j3ster2019/HF-PA-v10/FuturePowerControl/Screenshot_2023-09-25_10-48-14.png

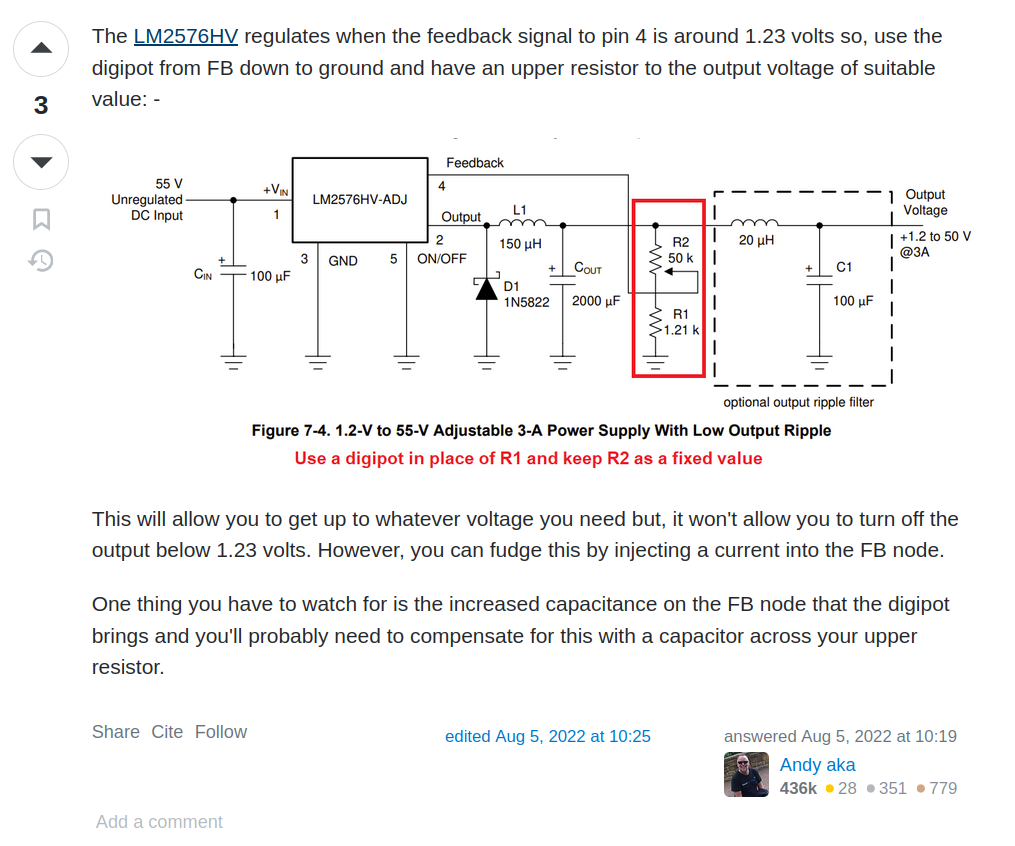
FuturePowerControl/Screenshot_2023-09-25_10-48-14.png
