j3ster2019/HF-PA-v10/Heat-Sinking/heatsinkmtg.gif

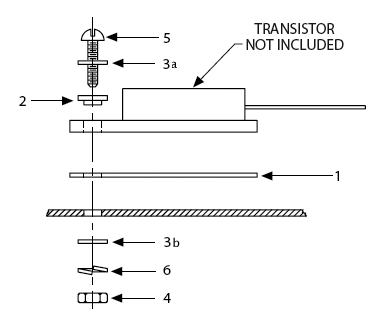
Heat-Sinking/heatsinkmtg.gif
