j3ster2019/HF-PA-v10/Heat-Sinking/heatsinkmtgparts.gif

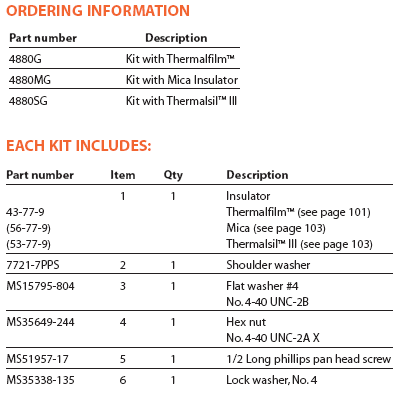
Heat-Sinking/heatsinkmtgparts.gif
