j3ster2019/HF-PA-v10/info/25wlinear-small.png

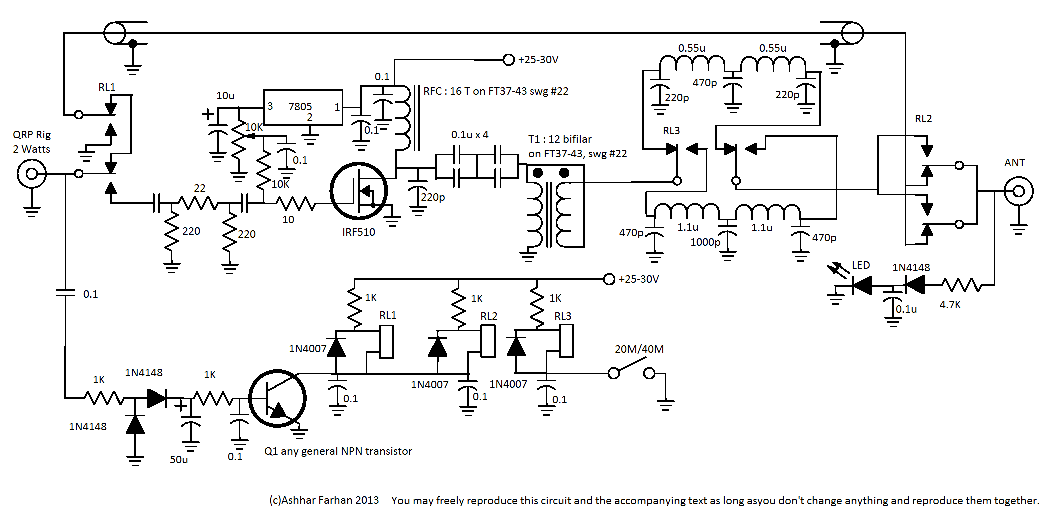
info/25wlinear-small.png
