j3ster2019/HF-PA-v10/info/Henning Paul's PA prototype.jpeg

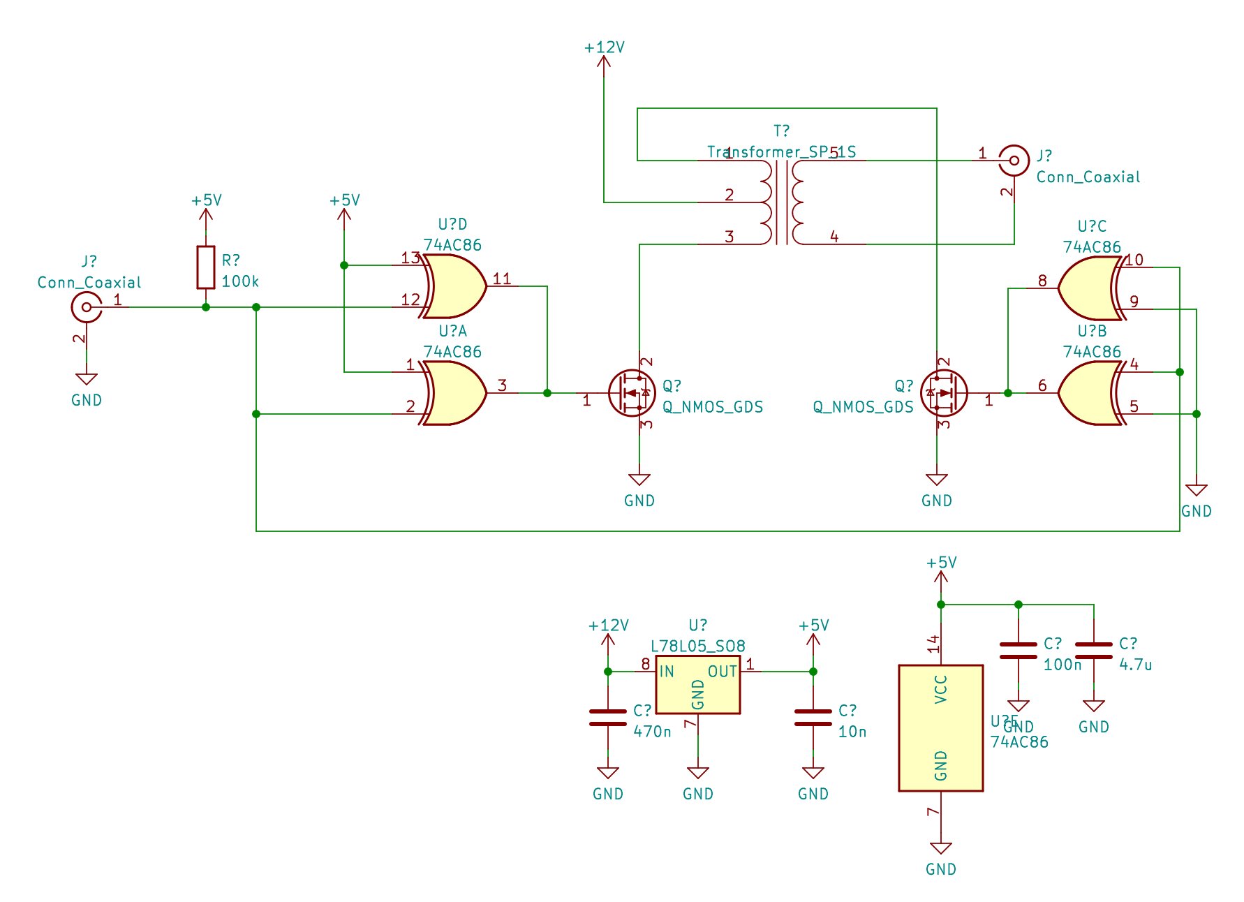
info/Henning Paul's PA prototype.jpeg
