j3ster2019/HF-PA-v10/info/Screenshot_2022-11-07_18-18-30.png

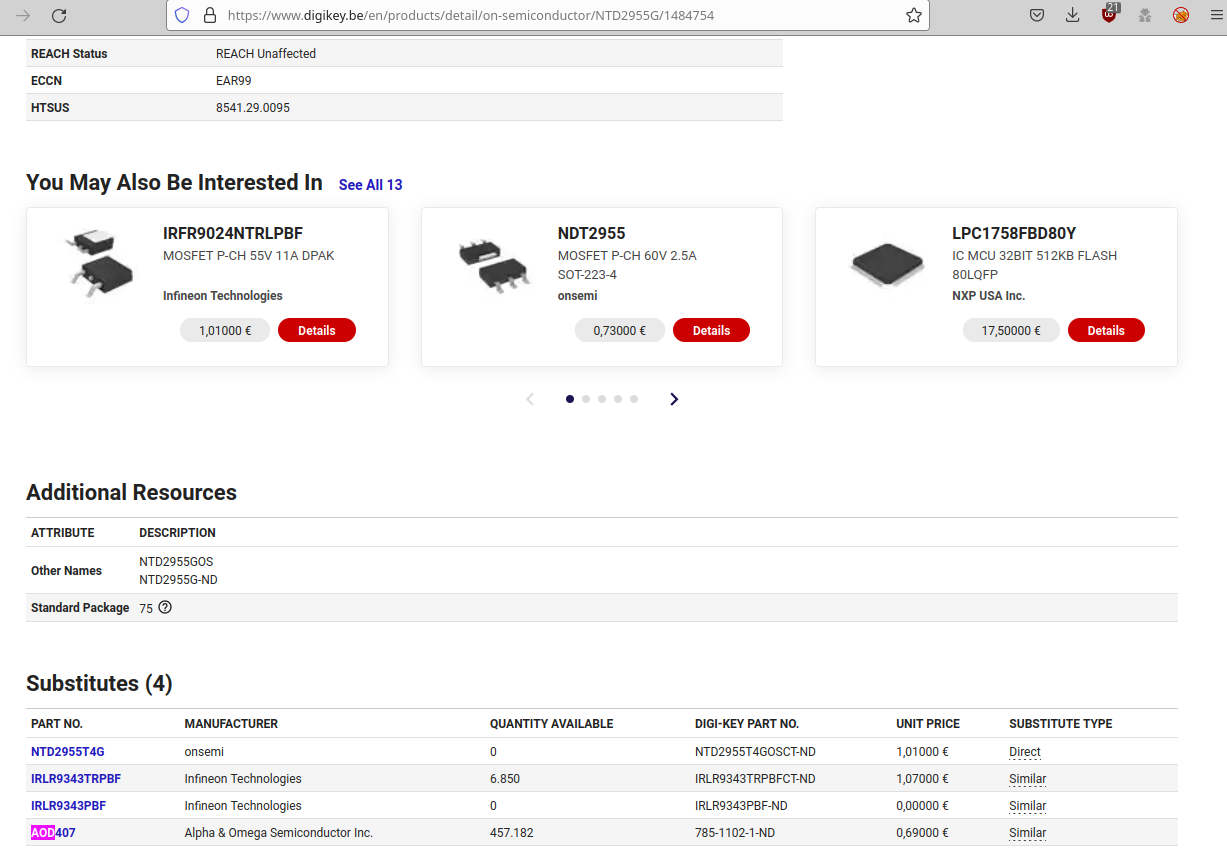
info/Screenshot_2022-11-07_18-18-30.png
