j3ster2019/HF-PA-v10/IRF530-Hack/Screenshot_2023-09-17_14-39-16.png

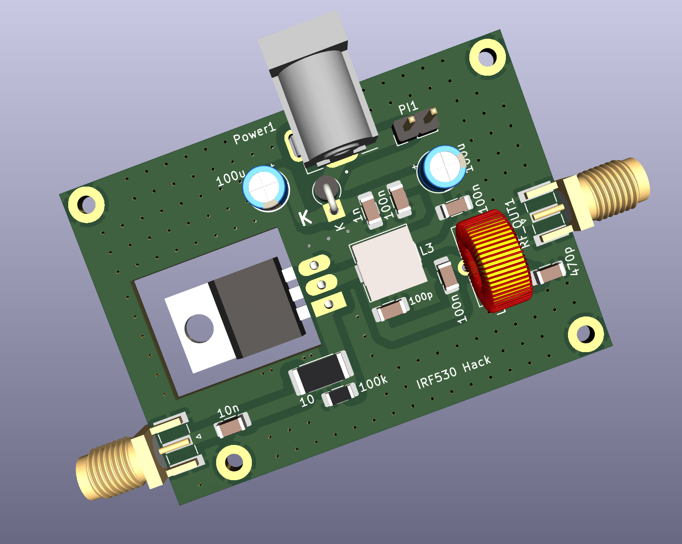
IRF530-Hack/Screenshot_2023-09-17_14-39-16.png
