j3ster2019/HF-PA-v10/IRFP-Hacks-v4/Screenshot_2024-04-25_09-21-08.png

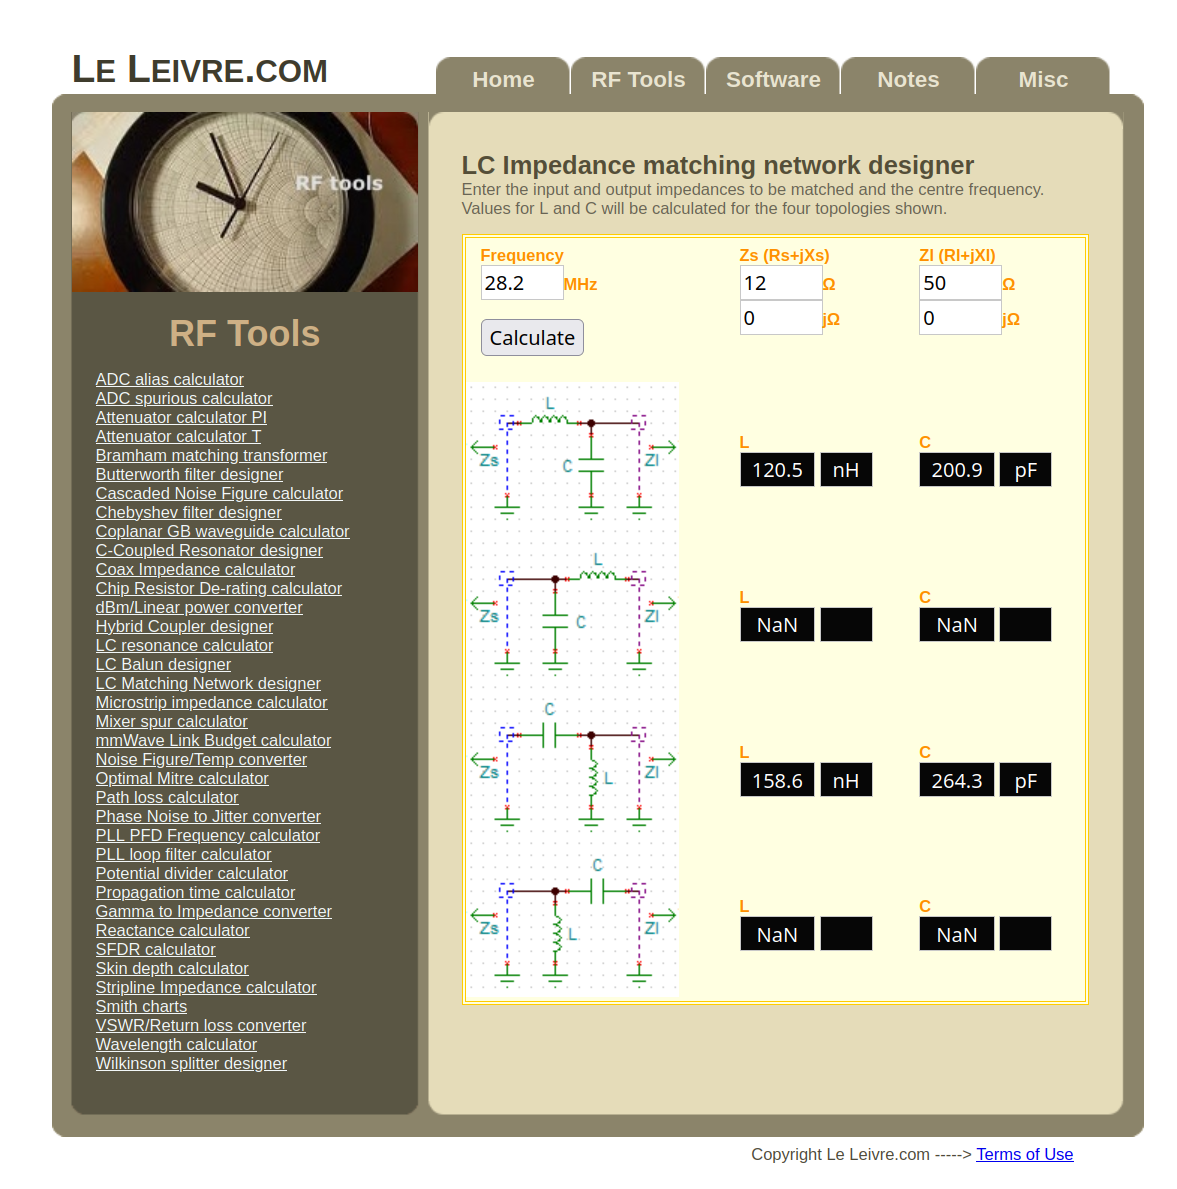
IRFP-Hacks-v4/Screenshot_2024-04-25_09-21-08.png
