j3ster2019/HF-PA-v10/IRFP-Hacks/Screenshot_2024-02-22_09-20-52.png

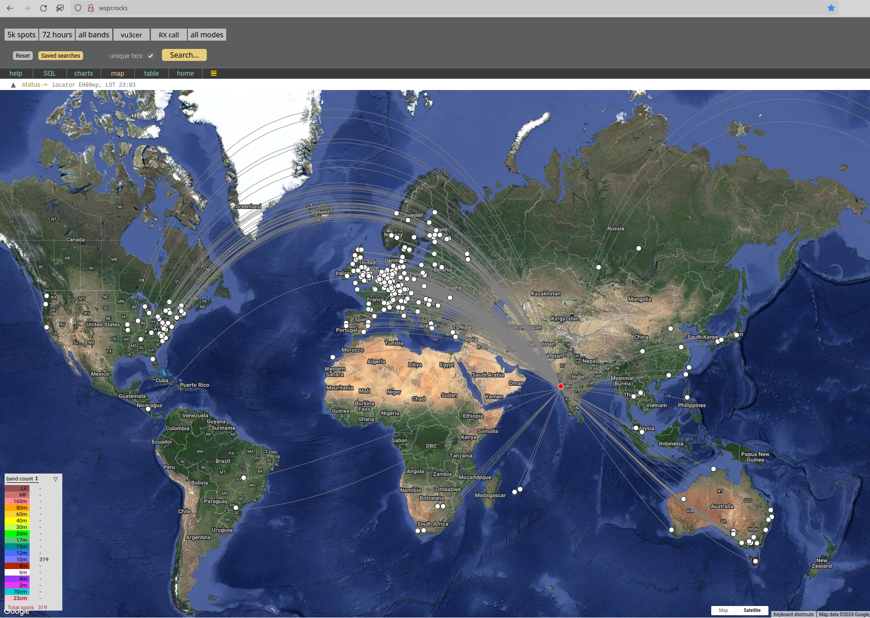
IRFP-Hacks/Screenshot_2024-02-22_09-20-52.png
