j3ster2019/HF-PA-v10/MRF101-Hack/7448510091.jpg

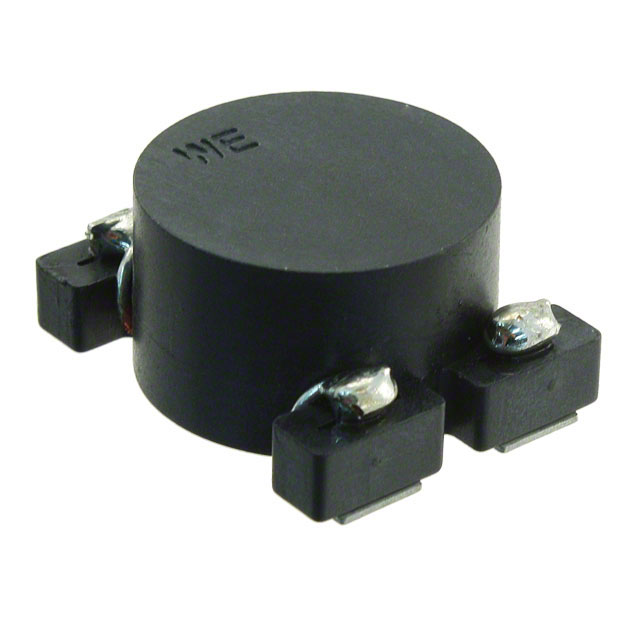
MRF101-Hack/7448510091.jpg
