j3ster2019/HF-PA-v10/R7/Screenshot_2023-10-06_10-12-58.png

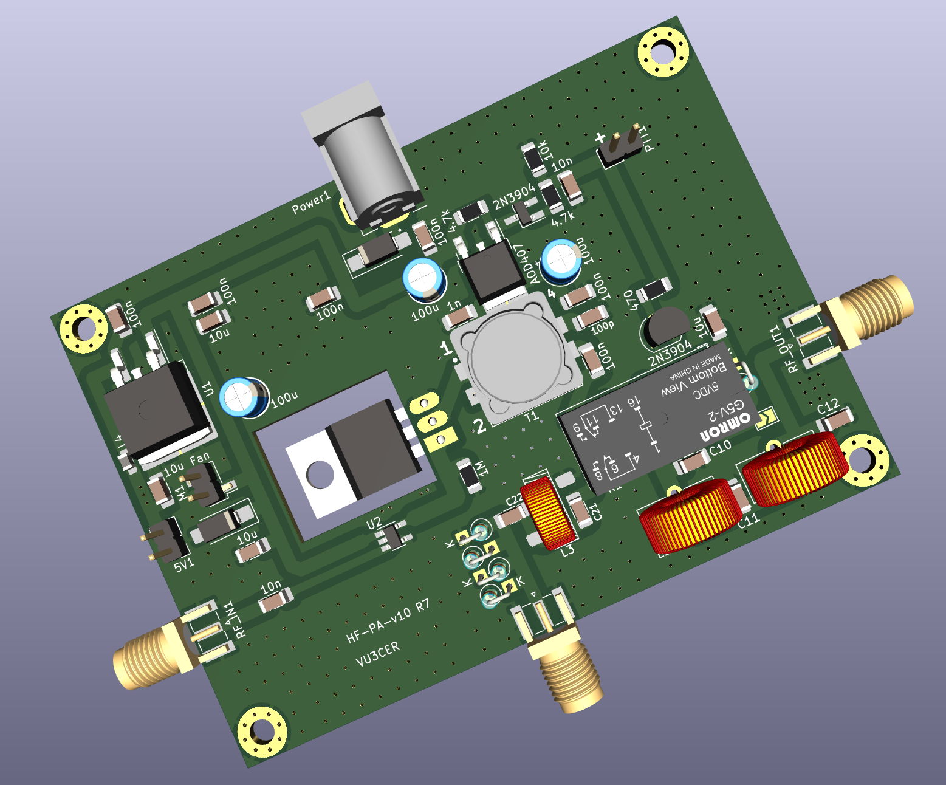
R7/Screenshot_2023-10-06_10-12-58.png
