j3ster2019/HF-PA-v10/v3-RD16HHF1/Screenshot_2023-09-16_10-33-11.png

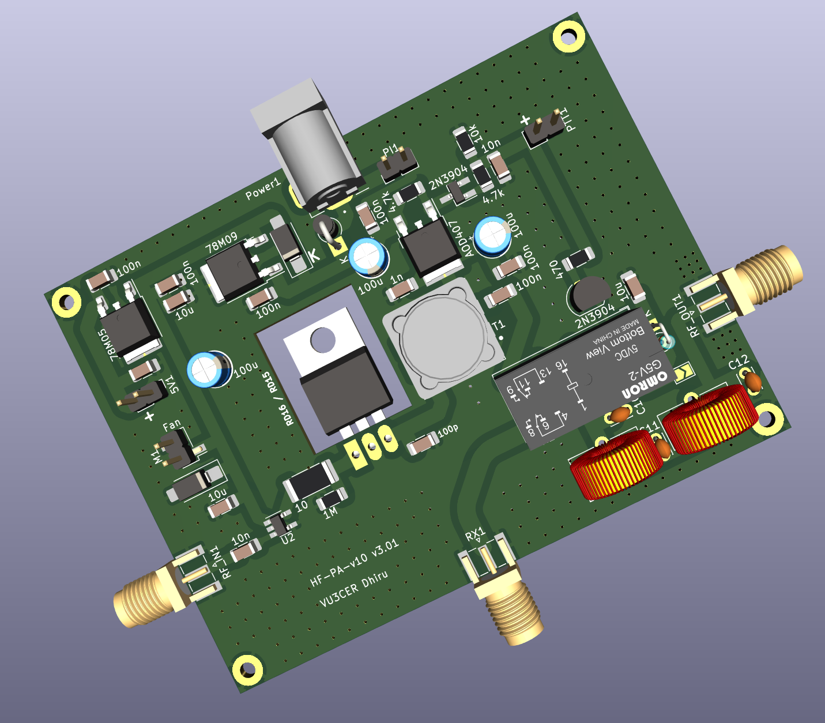
v3-RD16HHF1/Screenshot_2023-09-16_10-33-11.png
