j3ster2019/HF-PA-v10/IRFP-Hacks-v4/models/TO-220-3 Bend Mirror.stp

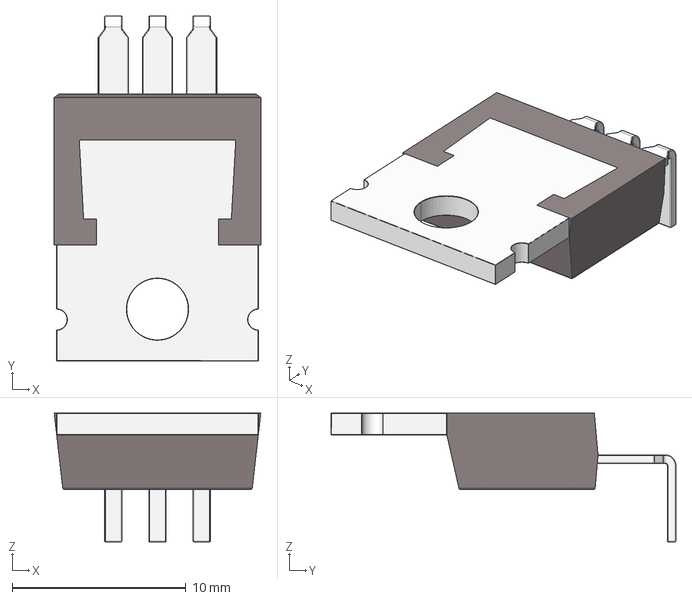
[picture p44: CAD file, 2024-05-09]
IRFP-Hacks-v4/models/TO-220-3 Bend Mirror.stp
11.9 x 19.8 x 7.41 mm
