j3ster2019/HF-PA-v10/MRF101-Hack/models/WE-CAIR_4248 (rev1).stp

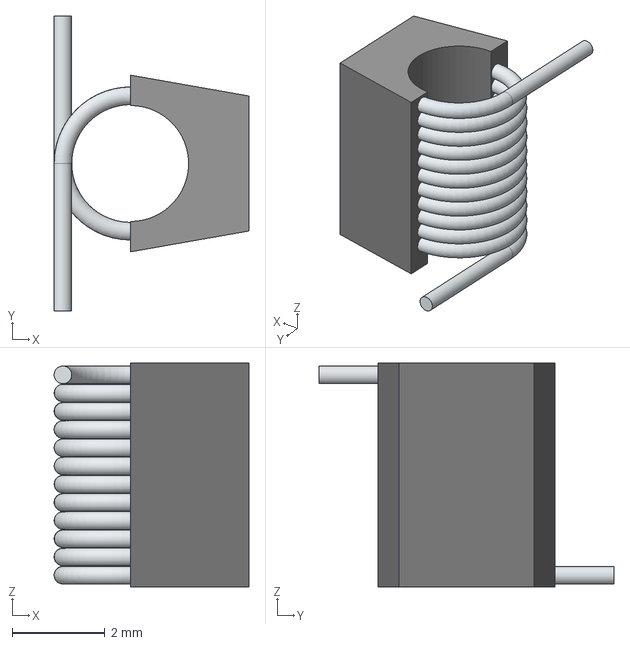
[picture p45: CAD file, 2024-05-09]
MRF101-Hack/models/WE-CAIR_4248 (rev1).stp
4.20 x 6.36 x 4.83 mm
