j3ster2019/HF-PA-v10/UCC-Driver-Board/models/Poti_10kohm.stp

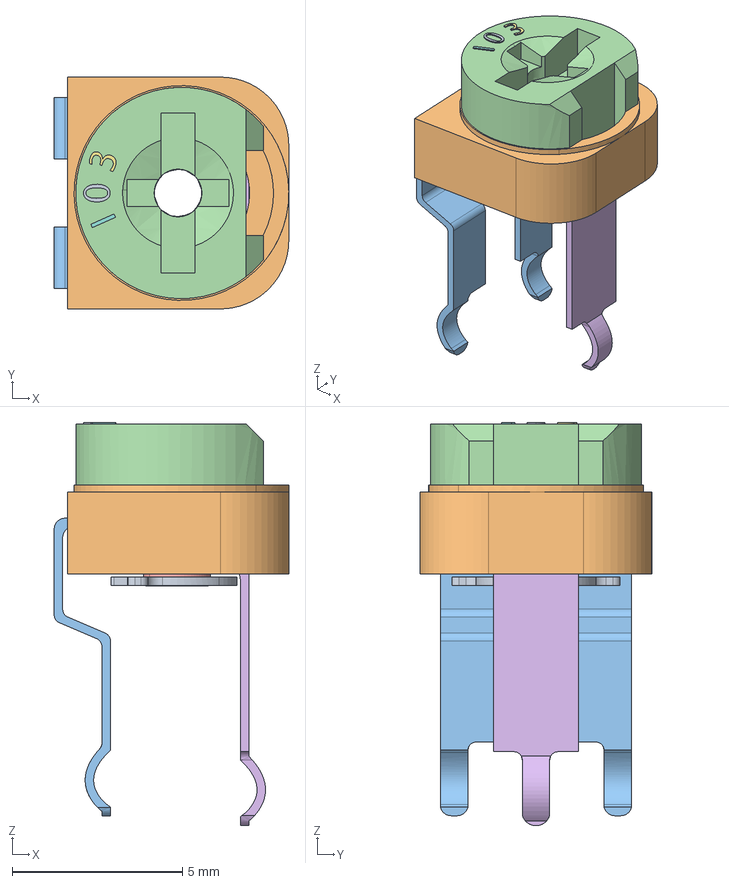
[picture p46: CAD file, 2024-05-09]
UCC-Driver-Board/models/Poti_10kohm.stp
6.88 x 6.80 x 11.8 mm
