j3ster2019/HF-PA-v10/MRF101-Hack/models/DG340-3.81-02P-12-00AH.STEP

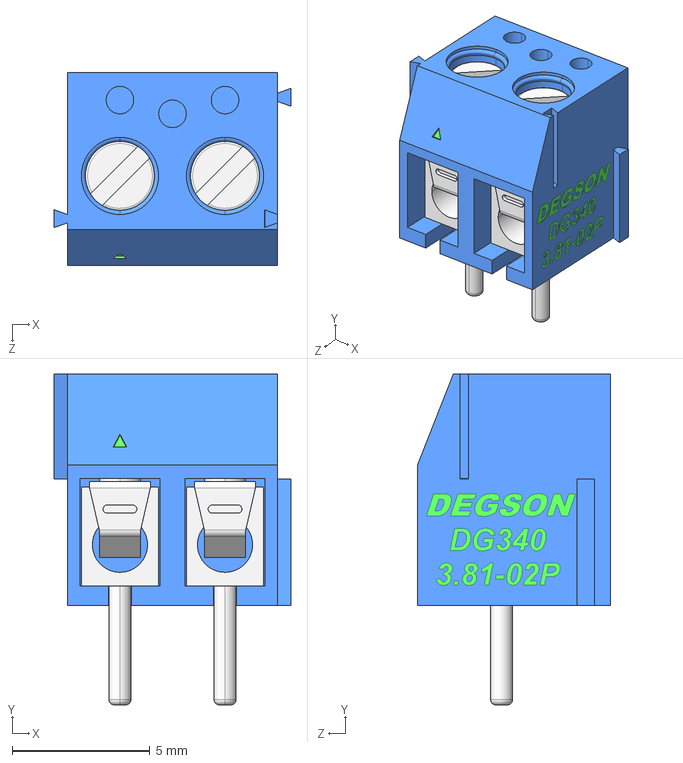
[picture p47: CAD file, 2024-05-09]
MRF101-Hack/models/DG340-3.81-02P-12-00AH.STEP
8.58 x 12.0 x 7.00 mm
