j3ster2019/HF-PA-v10/IRFP-Hacks-v4/models/Inductor_7x7x2.5.STEP

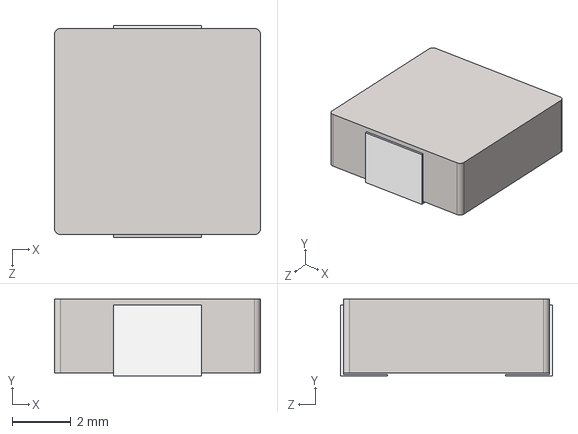
[picture p48: CAD file, 2024-05-09]
IRFP-Hacks-v4/models/Inductor_7x7x2.5.STEP
7.00 x 2.60 x 7.20 mm
