j3ster2019/HF-PA-v10/MRF101-Hack/models/User Library-3386P.STEP

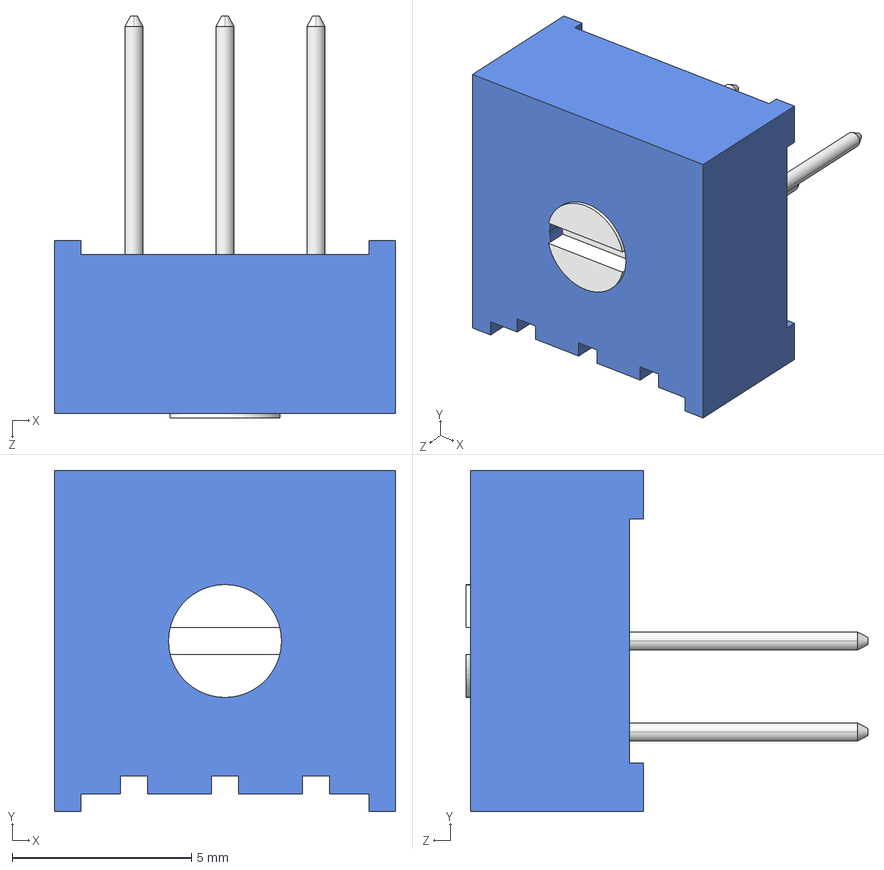
[picture p49: CAD file, 2024-05-09]
MRF101-Hack/models/User Library-3386P.STEP
9.53 x 9.53 x 11.2 mm
