j3ster2019/HF-PA-v10/results/Screenshot_2023-09-14_21-32-34.png

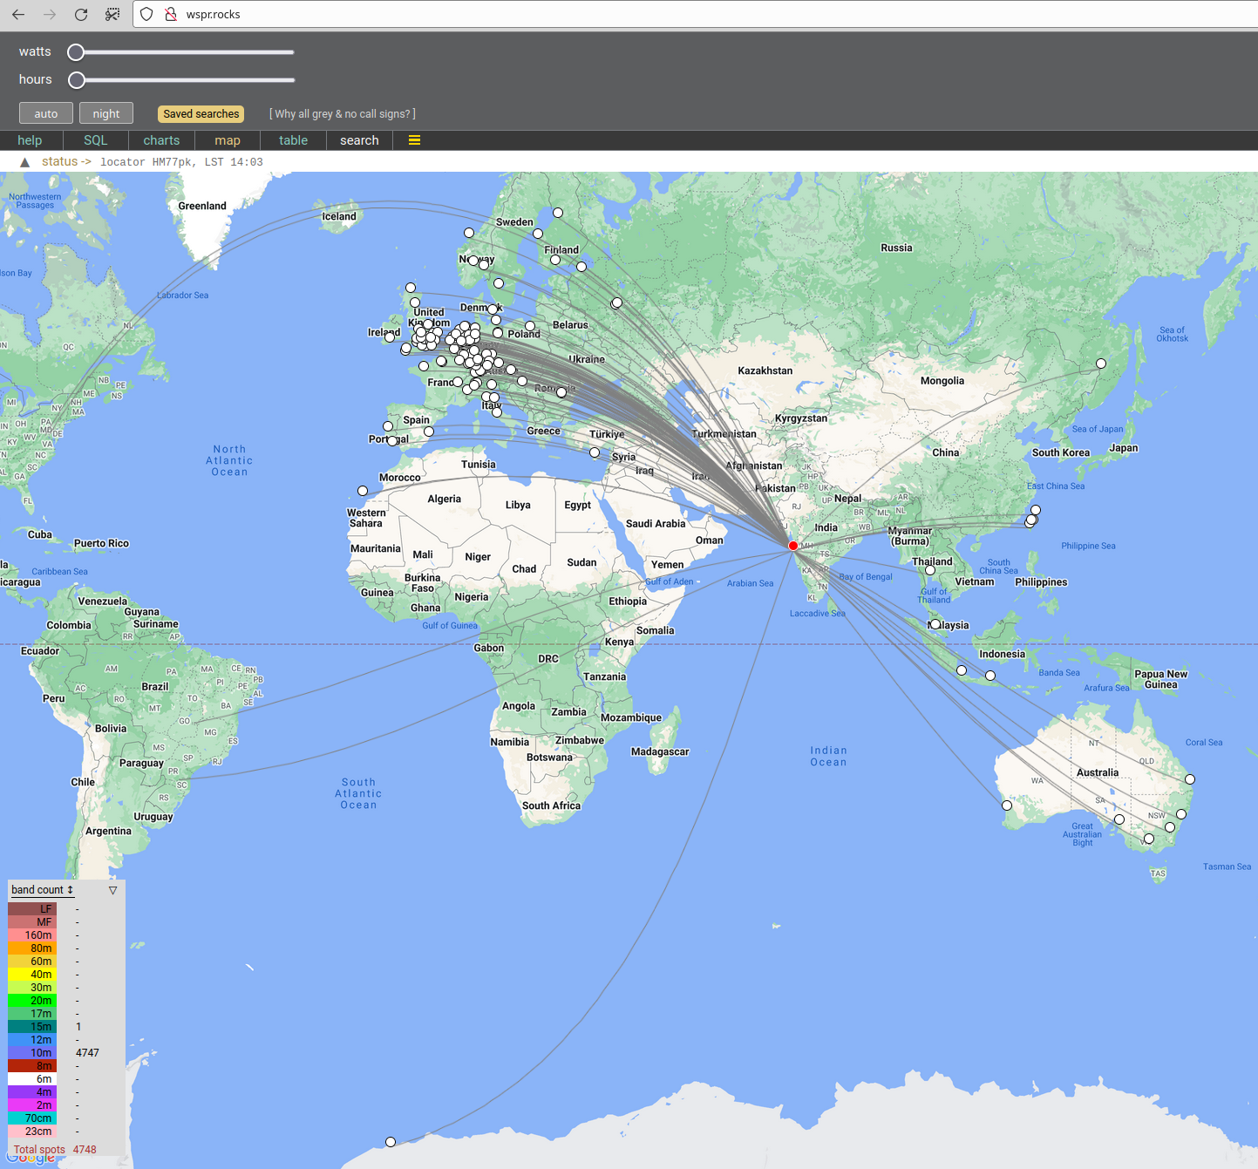
results/Screenshot_2023-09-14_21-32-34.png
