j3ster2019/HF-PA-v10/results/Screenshot_2023-11-05_21-15-48.png

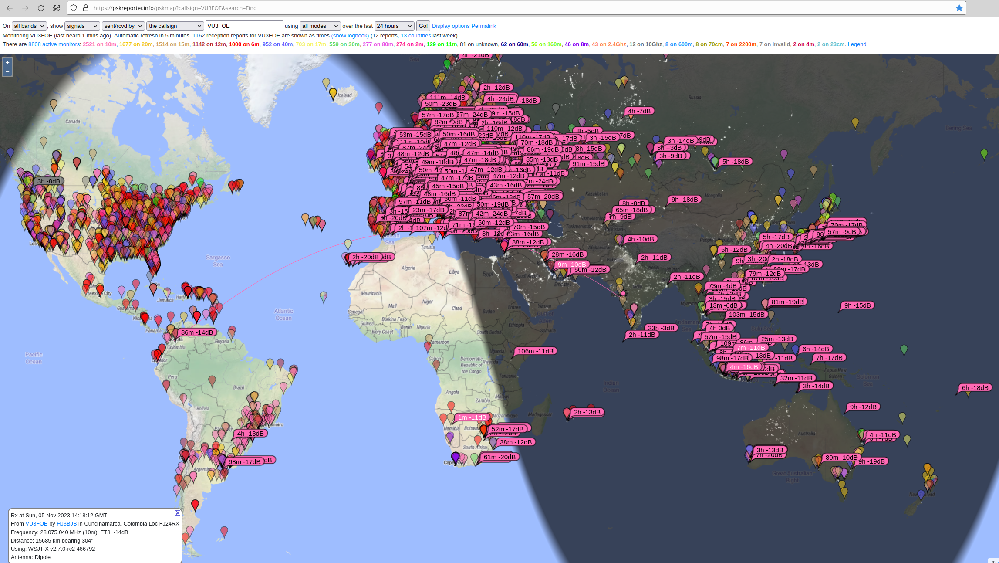
results/Screenshot_2023-11-05_21-15-48.png
