j3ster2019/HF-PA-v10/IRFP-Hacks/IRFP150-With-LC-Matching.asc

C1: cap; 120p
C2: cap; 10nF
C3: cap; 470pF
C4: cap; 10nF
C5: cap; 200pF
C6: cap; 120p
L1: ind; 240nH
L2: ind; 10µ
L3: ind; 360n
L4: ind; 360n
M1: nmos; IRFP140
R1: res; 10
R2: res; 50
R3: res; 100k
R4: res; 50
V1: voltage; PULSE(0 20 0 1n 1n {0.5*PERIOD} {PERIOD})
V2: voltage; 30
Named nets: 0, VIN, VGS
.param FREQ=14.100E6
.param PERIOD 1/{FREQ}
.tran 0 {1000*PERIOD} {996*PERIOD}
.inc RD16HHF1.txt
.meas Pin AVG -V(vin)*I(V2)
.meas Vmax MAX V(Vds)
.meas Pout AVG V(Vout)*I(R2)
.meas Ploss AVG V(Vds)*Id(M4)+V(Vgs)*Ig(M4)
.param Rl 100
.param Cl 391p
.param Ll 234n
