j3ster2019/HF-PA-v10/IRF530-Hack/HF-PA-v10.kicad_pcb

## KiCad design IRF530-Hack/HF-PA-v10.kicad_pcb (2024-05-09)

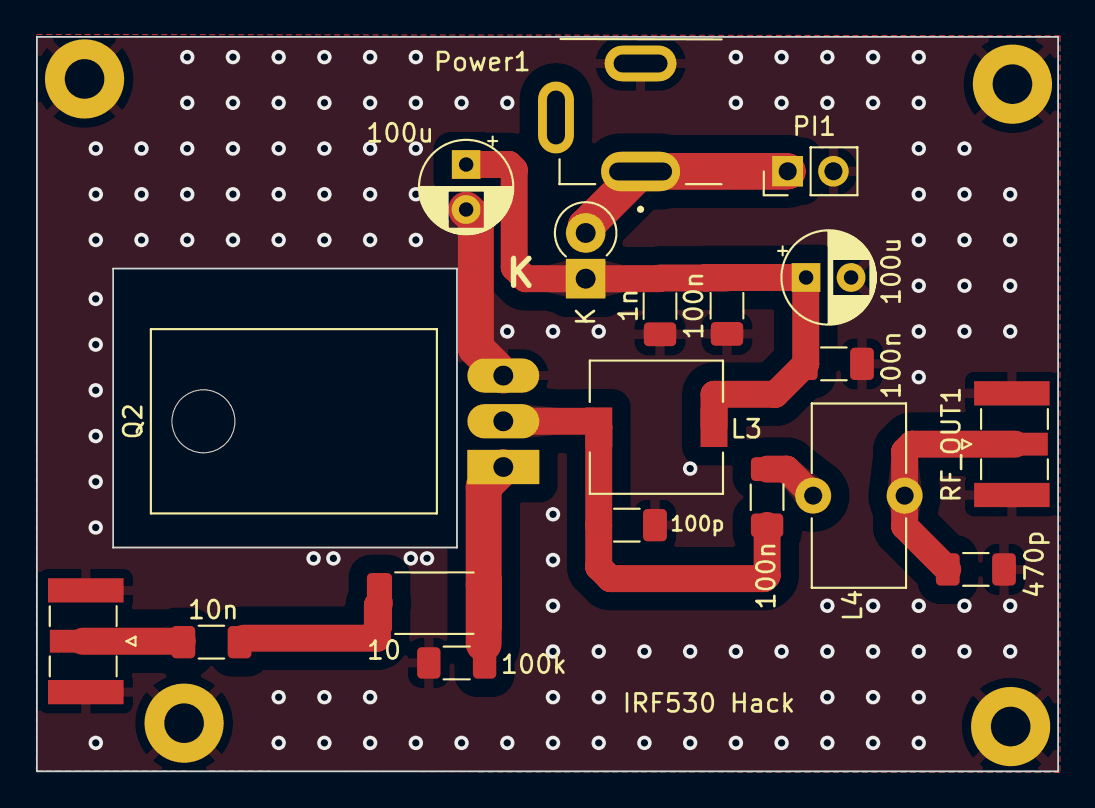
[picture p66: board IRF530-Hack/HF-PA-v10.kicad_pcb from above]

Board: 2 copper layers, 56.7 x 40.8 mm, 23 parts (0 on the bottom side), 9 nets.

Parts:
C1: 470p; C_1206_3216Metric_Pad1.33x1.80mm_HandSolder
C3: 100p; C_1206_3216Metric_Pad1.33x1.80mm_HandSolder
C5, C15: 100u; CP_Radial_D5.0mm_P2.50mm
C6, C7, C14: 100n; C_1206_3216Metric_Pad1.33x1.80mm_HandSolder
C17: 1n; C_1206_3216Metric_Pad1.33x1.80mm_HandSolder
C19: 10n; C_1206_3216Metric_Pad1.33x1.80mm_HandSolder
D4: 2A+ Schottky (1N5822 / SR2100); D_DO-41_SOD81_P2.54mm_Vertical_KathodeUp
H1, H2, H3, H4: MountingHole_Pad; MountingHole_2.2mm_M2_Pad
L3: 3.3uH / 4.7uH; L_7.3x7.3_H3.5
L4: 240n; L_Toroid_Vertical_L10.0mm_W5.0mm_P5.08mm
PI1: VDC; PinHeader_1x02_P2.54mm_Vertical
Power1: DC-005 (Barrel Jack); XKB_DC-005-5A-2.0_Modded
Q2: IRF530; TO-220-3_Horizontal_TabDown
R1: 100k; R_1206_3216Metric_Pad1.30x1.75mm_HandSolder
R3: 10; R_2512_6332Metric_Pad1.40x3.35mm_HandSolder
RF_IN1: SMA; SMA_Samtec_SMA-J-P-X-ST-EM1_EdgeMount
RF_OUT1: SMA; SMA_Samtec_SMA-J-P-X-ST-EM1_EdgeMount

Connections:
+VDC: D4.2 (A), PI1.1, Power1.1
/DRAIN: C3.1, C7.2, L3.2, Q2.2 (D)
GND: C1.2, C3.2, C5.2, C6.2, C14.2, C15.2, C17.2, H1.1, H2.1, H3.1, H4.1, PI1.2, Power1.2, Q2.3 (S), R1.2, RF_IN1.2 (Ext), RF_OUT1.2 (Ext)
unnamed: C7.1, L4.1
unnamed: C19.2, R3.2
unnamed: C5.1, C6.1, C14.1, C15.1, C17.1, D4.1 (K), L3.1
unnamed: Q2.1 (G), R1.1, R3.1
unnamed: C19.1, RF_IN1.1 (In)
unnamed: C1.1, L4.2, RF_OUT1.1 (In)
